marcinbor85/retroduino/firmware/examples/blink_advanced/src/types.h

#ifndef TYPES_H
#define TYPES_H

typedef signed char             int8_t;
typedef short int               int16_t;
typedef long int                int32_t;

typedef unsigned char           uint8_t;
typedef unsigned short int      uint16_t;
typedef unsigned long int       uint32_t;

#endif
